borti4938/Audio4OSSC/installation/A4_ExtMCLK/installation_mclk_10-v1.3.JPG

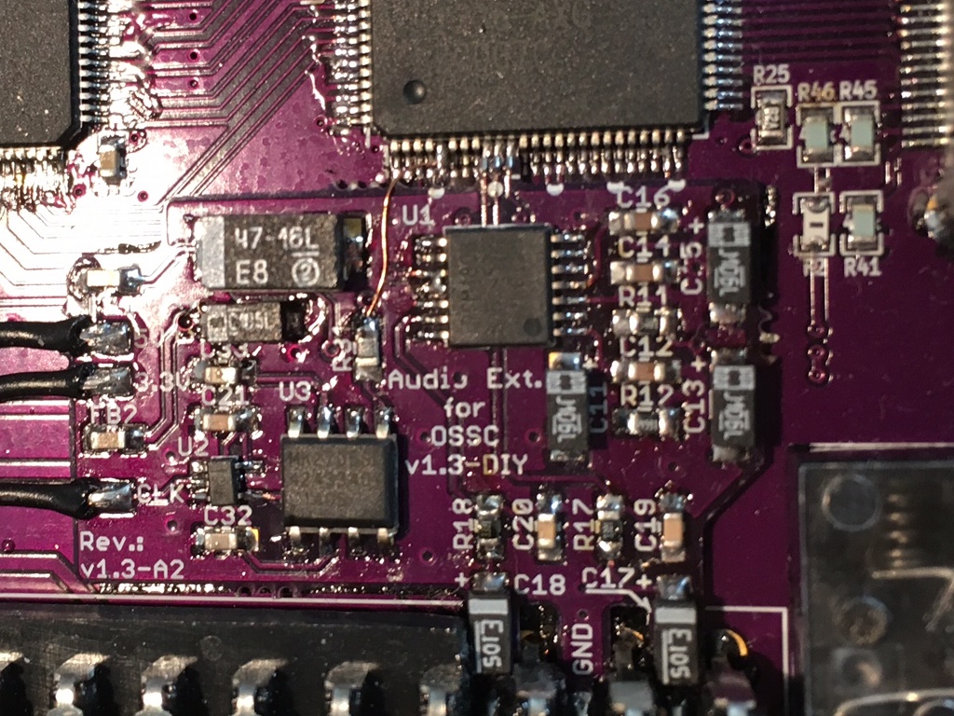
installation/A4_ExtMCLK/installation_mclk_10-v1.3.JPG
