borti4938/Audio4OSSC/installation/v1.3-A3/installation_ae_03.JPG

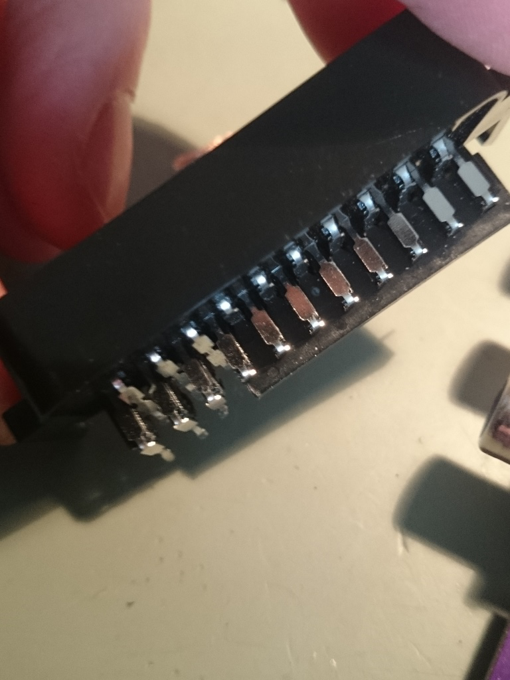
installation/v1.3-A3/installation_ae_03.JPG
