borti4938/Audio4OSSC/installation/v1.5-A3a/installation_ae_01.png

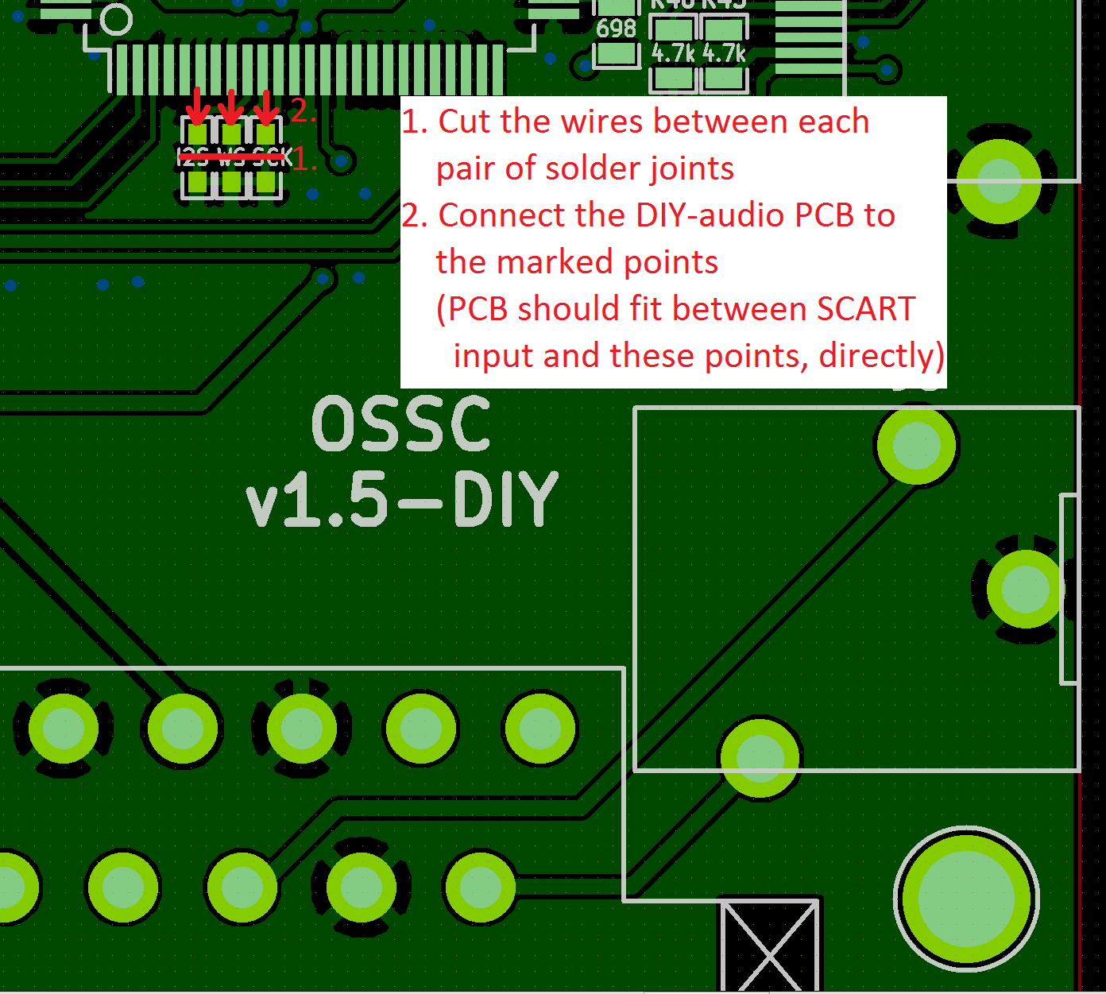
installation/v1.5-A3a/installation_ae_01.png
