borti4938/Audio4OSSC/installation/v1.5-A3a/installation_ae_04_05.JPG

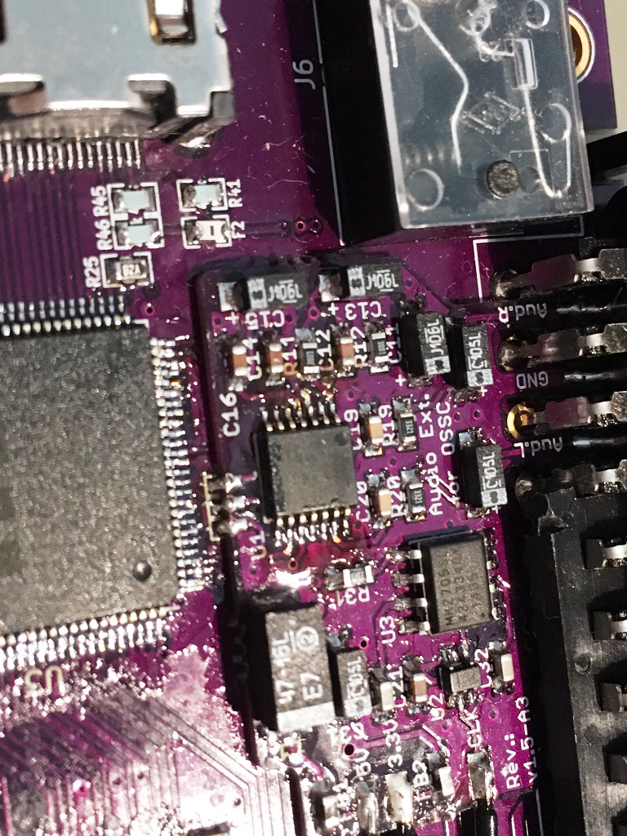
installation/v1.5-A3a/installation_ae_04_05.JPG
