borti4938/Audio4OSSC/installation/v1.5_A3b_VGP/installation_ae_06.jpg

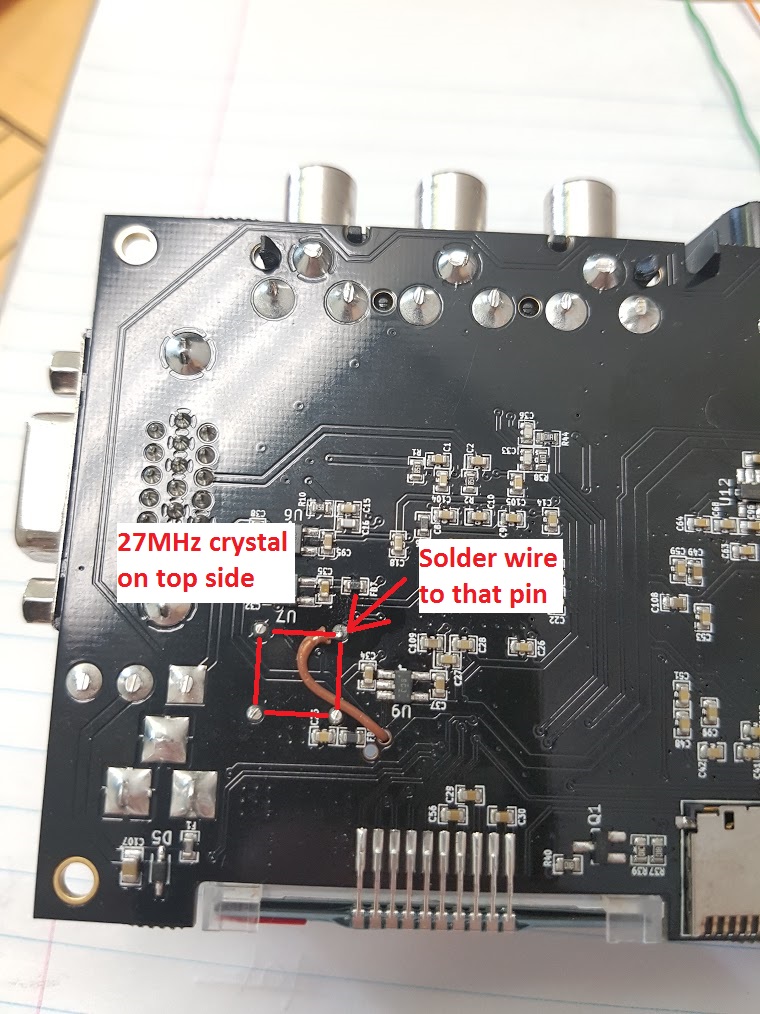
installation/v1.5_A3b_VGP/installation_ae_06.jpg
